Francois-Le/Keyboard/code/arduino_keyboard/keyboard.cpp

#include "keyboard.h"
#include "trace.h"

#include "PluggableUSBHID.h"
#include "platform/Stream.h"
#include "PlatformMutex.h"

#include "Keyboard.h"
#include "usb_phy_api.h"

namespace KeyboardImpl {
#define REPORT_ID_KEYBOARD 1
#define REPORT_ID_VOLUME 3

enum ModifierKeys {
  MOD_CTRL = 0x01,
  MOD_SHIFT = 0x02,
  MOD_ALT = 0x04,
  MOD_WIN = 0x08,
  MOD_RCTRL = 0x10,
  MOD_RSHIFT = 0x20,
  MOD_RALT = 0x40,
  MOD_RWIN = 0x80,
};

using namespace arduino;

class KeyboardHID : public USBHID {
public:
  KeyboardHID(uint16_t vendor_id = 0x1235, uint16_t product_id = 0x0050, uint16_t product_release = 0x0001);
  virtual ~KeyboardHID();

  void press(uint8_t *keys, uint8_t modifiers, uint8_t mediaKey);
  void releaseAll();

protected:
  virtual const uint8_t *report_desc() override;
  virtual const uint8_t *configuration_desc(uint8_t index) override;

private:
  uint8_t _configuration_descriptor[41];
};


KeyboardHID::KeyboardHID(uint16_t vendor_id, uint16_t product_id, uint16_t product_release)
  : USBHID(0, 0, vendor_id, product_id, product_release) {
}

KeyboardHID::~KeyboardHID() {
}


void KeyboardHID::press(uint8_t *keys, uint8_t modifiers, uint8_t mediaKey) {
  HID_REPORT report;
  report.data[0] = REPORT_ID_KEYBOARD;
  report.data[1] = modifiers;
  report.data[2] = 0;
  report.data[3] = keys[0];
  report.data[4] = keys[1];
  report.data[5] = keys[2];
  report.data[6] = keys[3];
  report.data[7] = keys[4];
  report.data[8] = keys[5];
  report.length = 9;
  uint32_t start = micros();
  const bool keyboardSent = send(&report);
  const uint32_t keyboardDuration = uint32_t(micros() - start);

  report.data[0] = REPORT_ID_VOLUME;
  report.data[1] = mediaKey;
  report.length = 2;
  start = micros();
  const bool mediaSent = send(&report);
  const uint32_t mediaDuration = uint32_t(micros() - start);
  Trace::output(keys, modifiers, mediaKey, keyboardSent, mediaSent, keyboardDuration, mediaDuration);
}

void KeyboardHID::releaseAll() {
  HID_REPORT report;
  report.data[0] = REPORT_ID_KEYBOARD;
  report.data[1] = 0;
  report.data[2] = 0;
  report.data[3] = 0;
  report.data[4] = 0;
  report.data[5] = 0;
  report.data[6] = 0;
  report.data[7] = 0;
  report.data[8] = 0;
  report.length = 9;

  const uint32_t start = micros();
  const bool sent = send(&report);
  Trace::hid(report.data, report.length, sent, uint32_t(micros() - start));
}

const uint8_t *KeyboardHID::report_desc() {
  static const uint8_t reportDescriptor[] = {
    USAGE_PAGE(1),
    0x01,  // Generic Desktop
    USAGE(1),
    0x06,  // Keyboard
    COLLECTION(1),
    0x01,  // Application
    REPORT_ID(1),
    REPORT_ID_KEYBOARD,

    USAGE_PAGE(1),
    0x07,  // Key Codes
    USAGE_MINIMUM(1),
    0xE0,
    USAGE_MAXIMUM(1),
    0xE7,
    LOGICAL_MINIMUM(1),
    0x00,
    LOGICAL_MAXIMUM(1),
    0x01,
    REPORT_SIZE(1),
    0x01,
    REPORT_COUNT(1),
    0x08,
    INPUT(1),
    0x02,  // Data, Variable, Absolute
    REPORT_COUNT(1),
    0x01,
    REPORT_SIZE(1),
    0x08,
    INPUT(1),
    0x01,  // Constant


    REPORT_COUNT(1),
    0x05,
    REPORT_SIZE(1),
    0x01,
    USAGE_PAGE(1),
    0x08,  // LEDs
    USAGE_MINIMUM(1),
    0x01,
    USAGE_MAXIMUM(1),
    0x05,
    OUTPUT(1),
    0x02,  // Data, Variable, Absolute
    REPORT_COUNT(1),
    0x01,
    REPORT_SIZE(1),
    0x03,
    OUTPUT(1),
    0x01,  // Constant


    REPORT_COUNT(1),
    0x06,
    REPORT_SIZE(1),
    0x08,
    LOGICAL_MINIMUM(1),
    0x00,
    LOGICAL_MAXIMUM(1),
    0x65,
    USAGE_PAGE(1),
    0x07,  // Key Codes
    USAGE_MINIMUM(1),
    0x00,
    USAGE_MAXIMUM(1),
    0x65,
    INPUT(1),
    0x00,  // Data, Array
    END_COLLECTION(0),

    // Media Control
    USAGE_PAGE(1),
    0x0C,
    USAGE(1),
    0x01,
    COLLECTION(1),
    0x01,
    REPORT_ID(1),
    REPORT_ID_VOLUME,
    USAGE_PAGE(1),
    0x0C,
    LOGICAL_MINIMUM(1),
    0x00,
    LOGICAL_MAXIMUM(1),
    0x01,
    REPORT_SIZE(1),
    0x01,
    REPORT_COUNT(1),
    0x07,
    USAGE(1),
    0xB5,  // Next Track
    USAGE(1),
    0xB6,  // Previous Track
    USAGE(1),
    0xB7,  // Stop
    USAGE(1),
    0xCD,  // Play / Pause
    USAGE(1),
    0xE2,  // Mute
    USAGE(1),
    0xE9,  // Volume Up
    USAGE(1),
    0xEA,  // Volume Down
    INPUT(1),
    0x02,  // Input (Data, Variable, Absolute)
    REPORT_COUNT(1),
    0x01,
    INPUT(1),
    0x01,
    END_COLLECTION(0),
  };
  reportLength = sizeof(reportDescriptor);
  return reportDescriptor;
}

#define DEFAULT_CONFIGURATION (1)
#define TOTAL_DESCRIPTOR_LENGTH ((1 * CONFIGURATION_DESCRIPTOR_LENGTH) \
                                 + (1 * INTERFACE_DESCRIPTOR_LENGTH) \
                                 + (1 * HID_DESCRIPTOR_LENGTH) \
                                 + (2 * ENDPOINT_DESCRIPTOR_LENGTH))

const uint8_t *KeyboardHID::configuration_desc(uint8_t index) {
  if (index != 0) {
    return NULL;
  }
  uint8_t configuration_descriptor_temp[] = {
    CONFIGURATION_DESCRIPTOR_LENGTH,  // bLength
    CONFIGURATION_DESCRIPTOR,         // bDescriptorType
    LSB(TOTAL_DESCRIPTOR_LENGTH),     // wTotalLength (LSB)
    MSB(TOTAL_DESCRIPTOR_LENGTH),     // wTotalLength (MSB)
    0x01,                             // bNumInterfaces
    DEFAULT_CONFIGURATION,            // bConfigurationValue
    0x00,                             // iConfiguration
    C_RESERVED | C_SELF_POWERED,      // bmAttributes
    C_POWER(0),                       // bMaxPower

    INTERFACE_DESCRIPTOR_LENGTH,  // bLength
    INTERFACE_DESCRIPTOR,         // bDescriptorType
    0x00,                         // bInterfaceNumber
    0x00,                         // bAlternateSetting
    0x02,                         // bNumEndpoints
    HID_CLASS,                    // bInterfaceClass
    HID_SUBCLASS_BOOT,            // bInterfaceSubClass
    HID_PROTOCOL_KEYBOARD,        // bInterfaceProtocol
    0x00,                         // iInterface

    HID_DESCRIPTOR_LENGTH,                 // bLength
    HID_DESCRIPTOR,                        // bDescriptorType
    LSB(HID_VERSION_1_11),                 // bcdHID (LSB)
    MSB(HID_VERSION_1_11),                 // bcdHID (MSB)
    0x00,                                  // bCountryCode
    0x01,                                  // bNumDescriptors
    REPORT_DESCRIPTOR,                     // bDescriptorType
    (uint8_t)(LSB(report_desc_length())),  // wDescriptorLength (LSB)
    (uint8_t)(MSB(report_desc_length())),  // wDescriptorLength (MSB)

    ENDPOINT_DESCRIPTOR_LENGTH,  // bLength
    ENDPOINT_DESCRIPTOR,         // bDescriptorType
    _int_in,                     // bEndpointAddress
    E_INTERRUPT,                 // bmAttributes
    LSB(MAX_HID_REPORT_SIZE),    // wMaxPacketSize (LSB)
    MSB(MAX_HID_REPORT_SIZE),    // wMaxPacketSize (MSB)
    1,                           // bInterval (milliseconds)

    ENDPOINT_DESCRIPTOR_LENGTH,  // bLength
    ENDPOINT_DESCRIPTOR,         // bDescriptorType
    _int_out,                    // bEndpointAddress
    E_INTERRUPT,                 // bmAttributes
    LSB(MAX_HID_REPORT_SIZE),    // wMaxPacketSize (LSB)
    MSB(MAX_HID_REPORT_SIZE),    // wMaxPacketSize (MSB)
    1,                           // bInterval (milliseconds)
  };
  MBED_ASSERT(sizeof(configuration_descriptor_temp) == sizeof(_configuration_descriptor));
  memcpy(_configuration_descriptor, configuration_descriptor_temp, sizeof(_configuration_descriptor));
  return _configuration_descriptor;
}

KeyboardHID s_keyboard;


uint8_t s_modifiers = 0;
uint8_t s_keys[6] = { 0, 0, 0, 0, 0, 0 };
int s_nextKey = 0;
uint8_t s_mediaKeys = 0;
}

void KeyboardOutput::add(Key k) {
  using namespace KeyboardImpl;
  switch (k) {
    case Key::CTRL: s_modifiers = s_modifiers | MOD_CTRL; break;
    case Key::SHIFT: s_modifiers = s_modifiers | MOD_SHIFT; break;
    case Key::ALT: s_modifiers = s_modifiers | MOD_ALT; break;
    case Key::WIN: s_modifiers = s_modifiers | MOD_WIN; break;
    case Key::RCTRL: s_modifiers = s_modifiers | MOD_RCTRL; break;
    case Key::RSHIFT: s_modifiers = s_modifiers | MOD_RSHIFT; break;
    case Key::RALT: s_modifiers = s_modifiers | MOD_RALT; break;
    case Key::RWIN: s_modifiers = s_modifiers | MOD_RWIN; break;

    default:
      if (s_nextKey < 6) {
        s_keys[s_nextKey] = uint8_t(k);
        s_nextKey++;
      }
      break;
  }
}

void KeyboardOutput::add(MediaKey k) {
  using namespace KeyboardImpl;
  s_mediaKeys = uint8_t(k);
}

void KeyboardOutput::releaseAll() {
  using namespace KeyboardImpl;
  s_modifiers = 0;
  for (uint8_t &key : s_keys) key = 0;
  s_nextKey = 0;
  s_mediaKeys = 0;
}

void KeyboardOutput::send() {
  using namespace KeyboardImpl;
  s_keyboard.press(s_keys, s_modifiers, s_mediaKeys);

  debugPrint("\tSending event: ");
  ON_DEBUG(print());
  debugPrintln();
}

bool KeyboardOutput::isAnyKeyPressed() {
  using namespace KeyboardImpl;
  return s_modifiers != 0 || s_nextKey != 0;
}

#if DEBUG_LOG
void KeyboardOutput::print() {
  using namespace KeyboardImpl;
  debugPrint("KeyboardOutput(modifiers: ");
  if (s_modifiers & MOD_CTRL) debugPrint("Ctrl ");
  if (s_modifiers & MOD_SHIFT) debugPrint("Shift ");
  if (s_modifiers & MOD_ALT) debugPrint("Alt ");
  if (s_modifiers & MOD_WIN) debugPrint("Win ");
  if (s_modifiers & MOD_RCTRL) debugPrint("Left_Ctrl ");
  if (s_modifiers & MOD_RSHIFT) debugPrint("Left_Shift ");
  if (s_modifiers & MOD_RALT) debugPrint("Left_Alt ");
  if (s_modifiers & MOD_RWIN) debugPrint("Left_Win ");
  debugPrint("keys: ");
  debugPrint(s_keys[0]);
  debugPrint(" ");
  debugPrint(s_keys[1]);
  debugPrint(" ");
  debugPrint(s_keys[2]);
  debugPrint(" ");
  debugPrint(s_keys[3]);
  debugPrint(" ");
  debugPrint(s_keys[4]);
  debugPrint(" ");
  debugPrint(s_keys[5]);
  debugPrint(" media_key: ");
  debugPrint(s_mediaKeys);
  debugPrint(")");
}
#endif
